DoganM95/TPS61040-Step-Up-Converter/assets/1.1-bottom.png

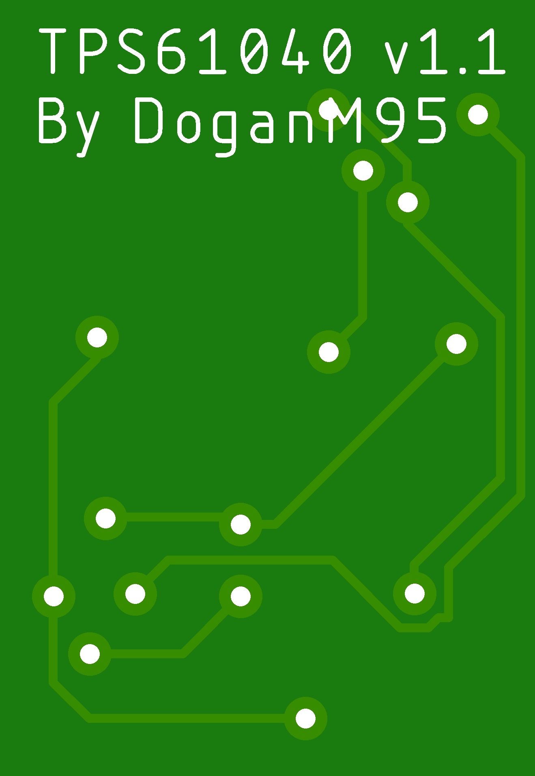
assets/1.1-bottom.png
